telzo2000/cool836A/img/IMG_0007.JPG

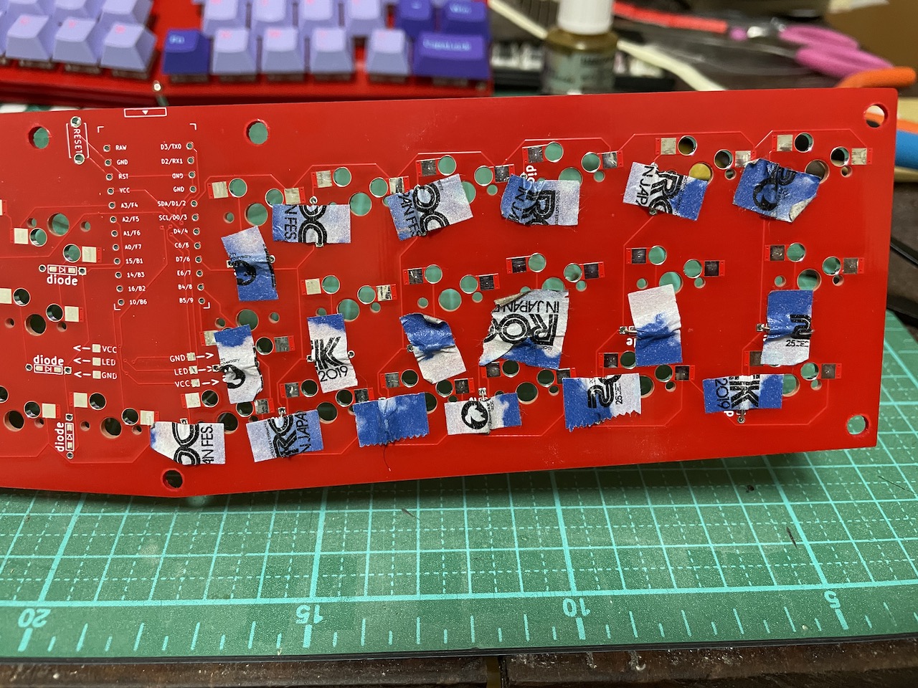
img/IMG_0007.JPG
