telzo2000/cool836A/img/IMG_0009.JPG

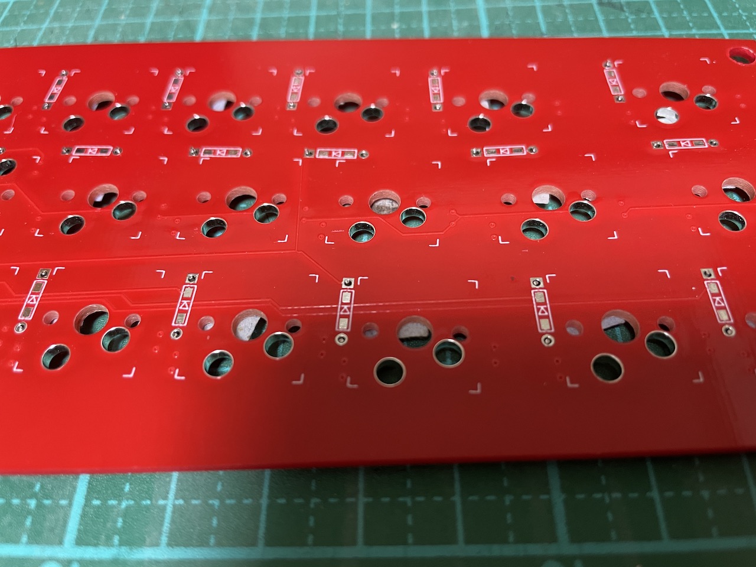
img/IMG_0009.JPG
