telzo2000/cool836A/img/IMG_0012.JPG

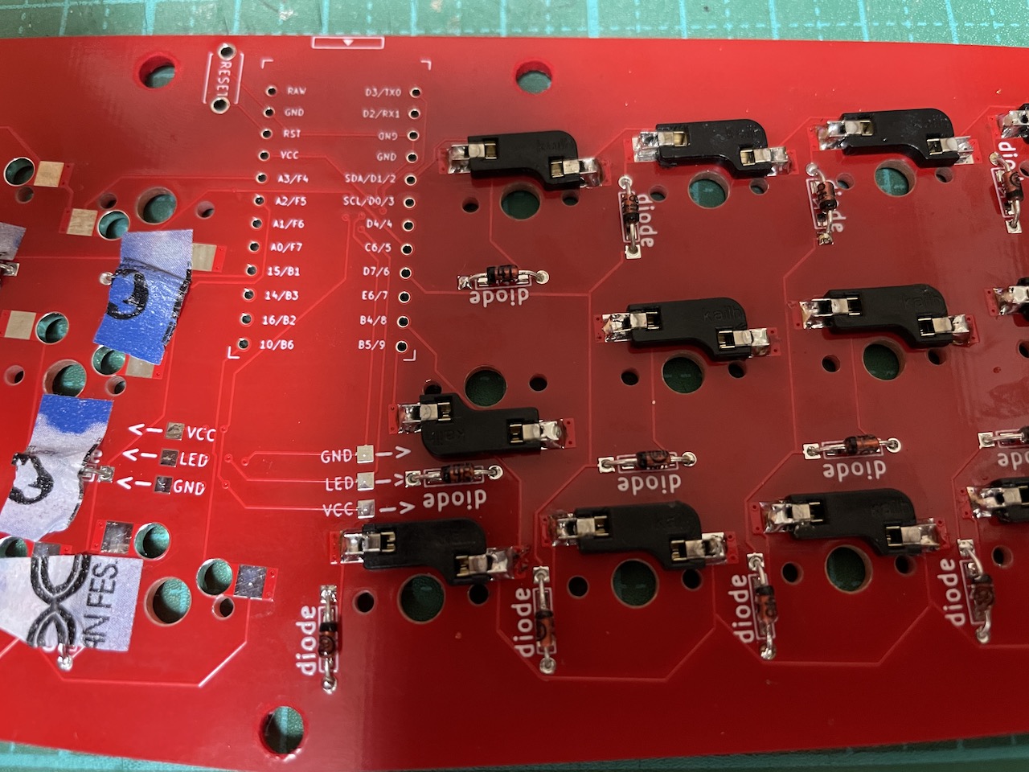
img/IMG_0012.JPG
