telzo2000/cool836A/img/IMG_0238.JPG

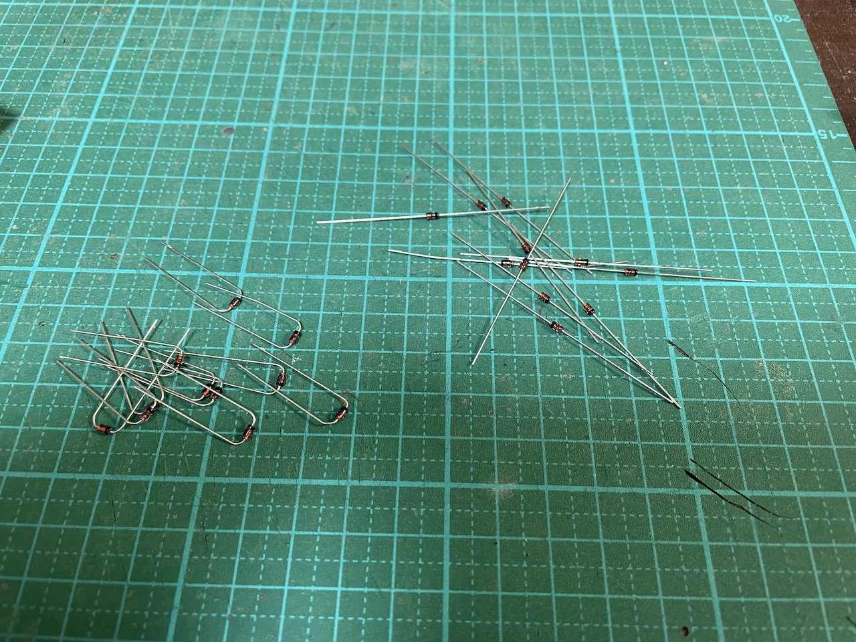
img/IMG_0238.JPG
